ThinhLe279/Battery-Management-System/Design/PCB/PCB.jpg

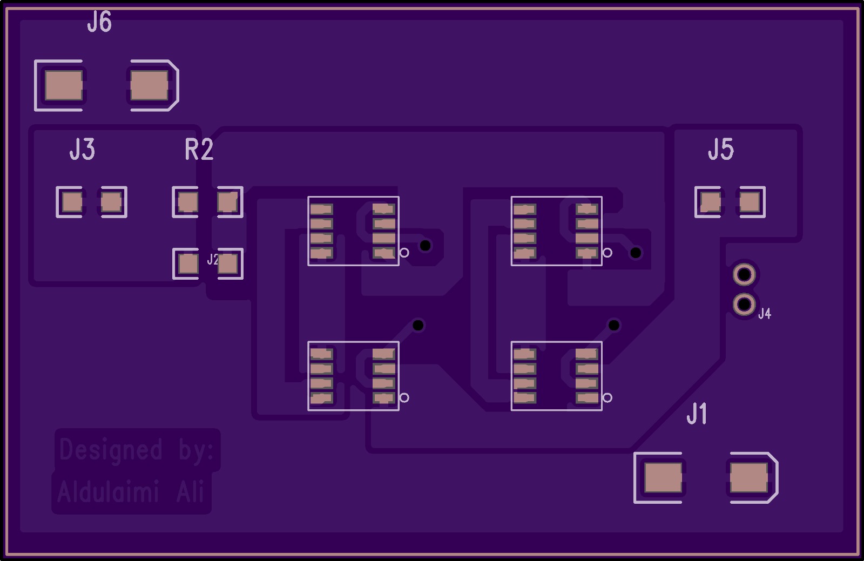
Design/PCB/PCB.jpg
