ThinhLe279/Battery-Management-System/schematic/IMG/Battery Balancing.png

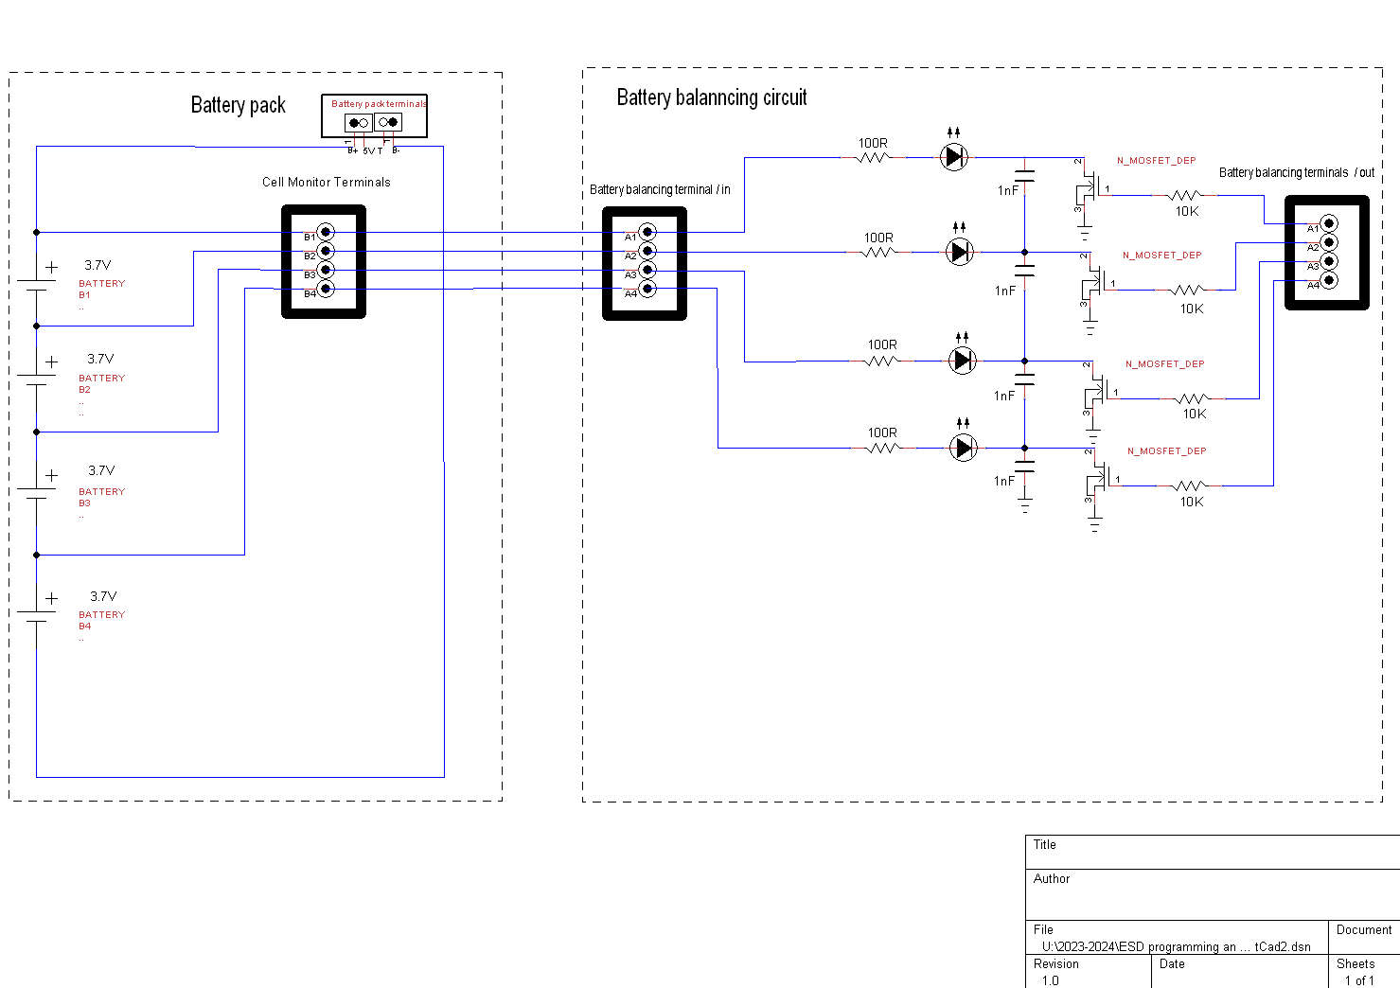
schematic/IMG/Battery Balancing.png
