ThinhLe279/Battery-Management-System/schematic/IMG/MCU power control.png

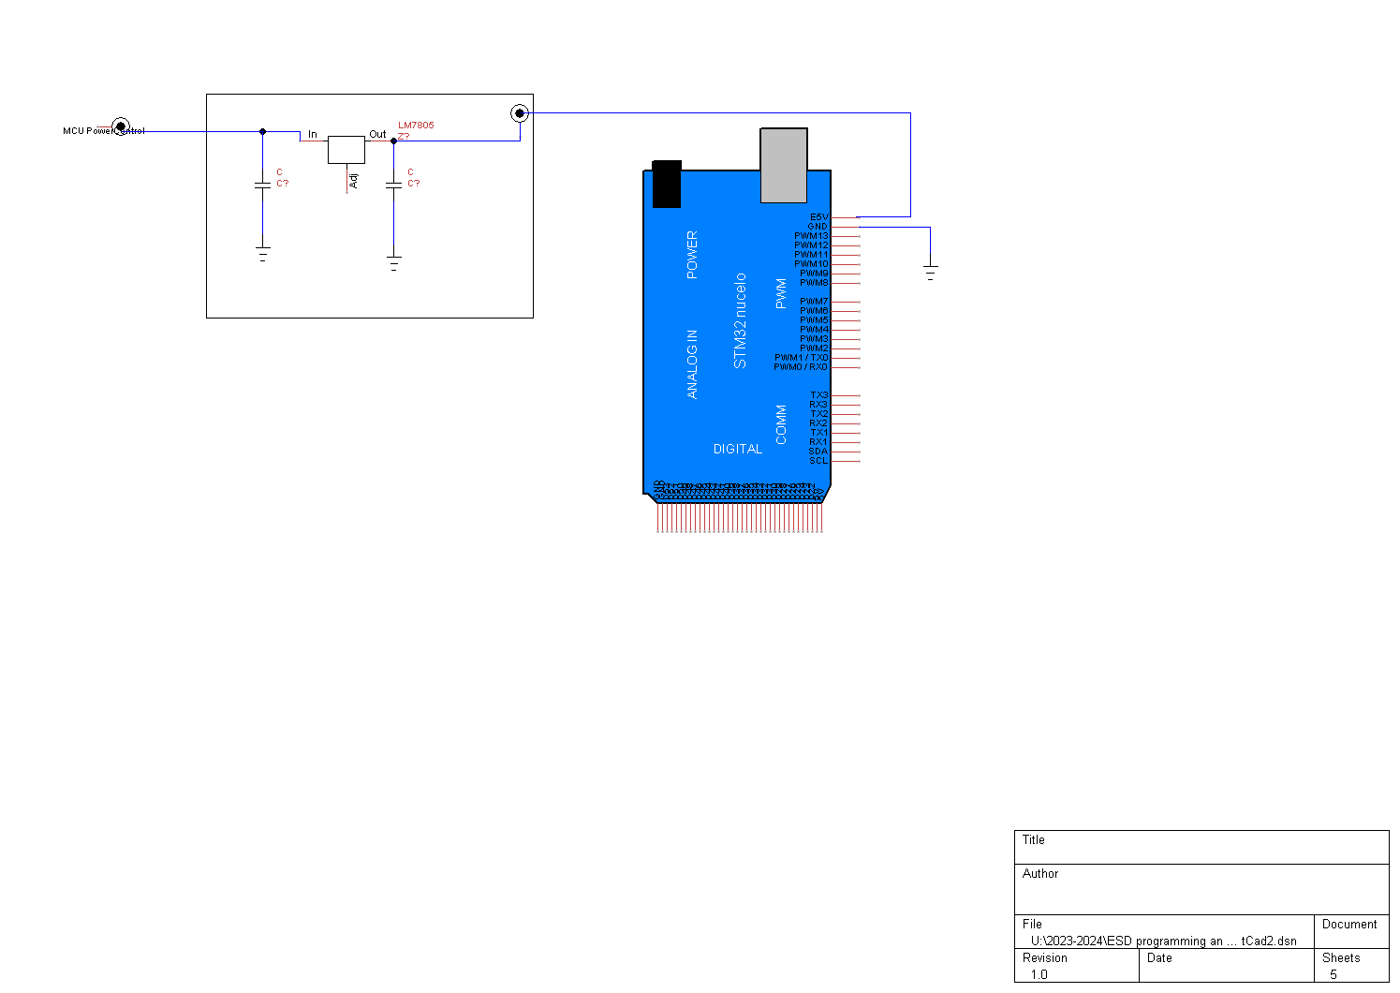
schematic/IMG/MCU power control.png
