ThinhLe279/Battery-Management-System/schematic/IMG/OP-AMP circuit.png

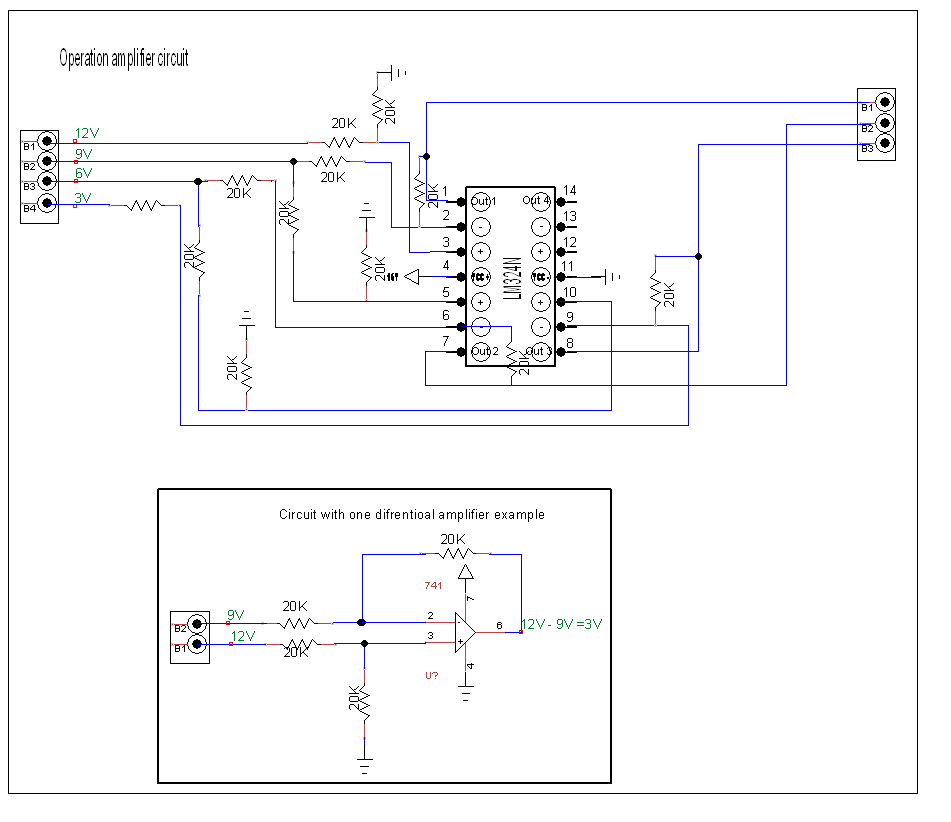
schematic/IMG/OP-AMP circuit.png
