ThinhLe279/Battery-Management-System/Simulation/15_5_voltage_output.PNG

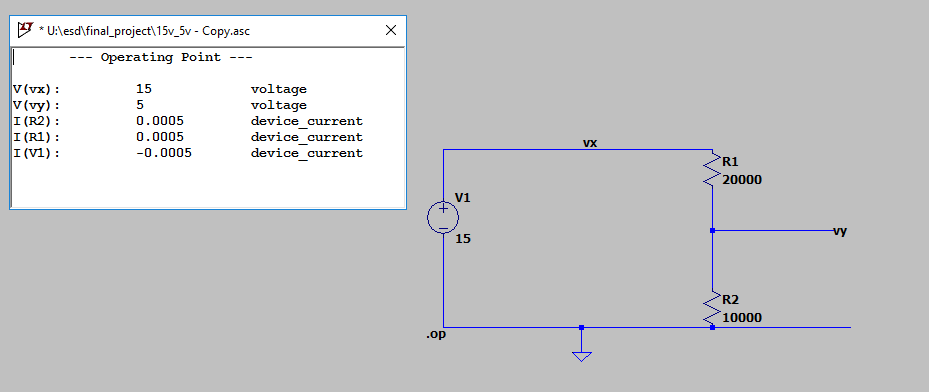
Simulation/15_5_voltage_output.PNG
