ThinhLe279/Battery-Management-System/Simulation/Simulation.PNG

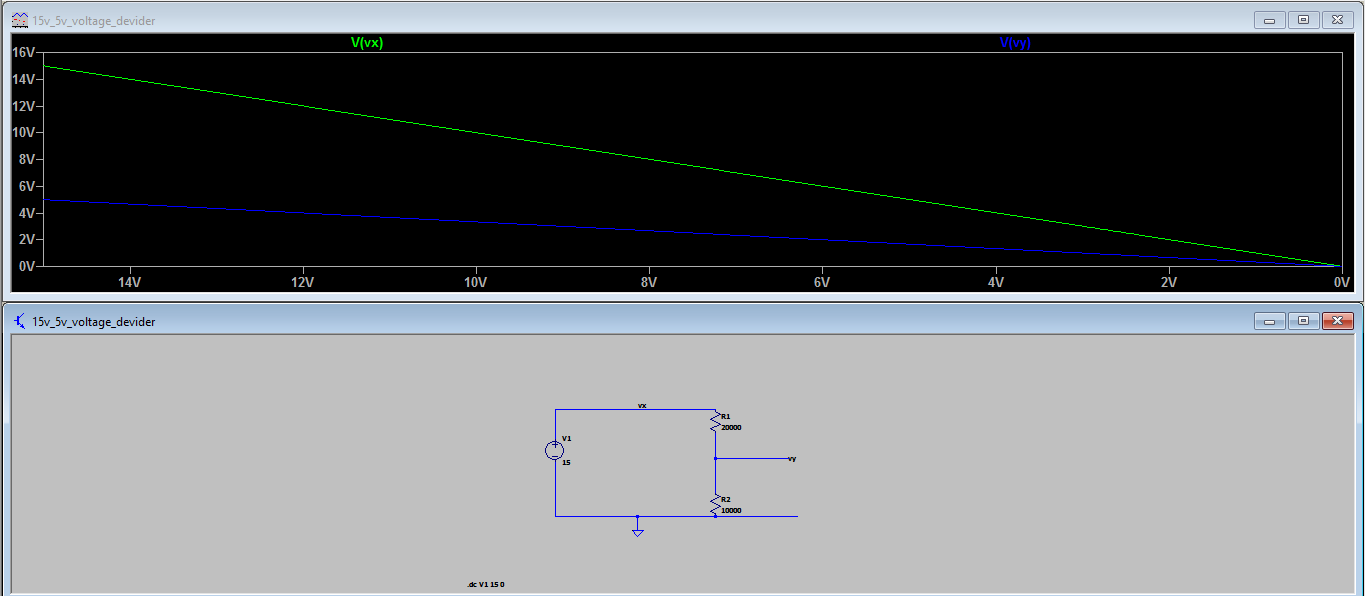
Simulation/Simulation.PNG
