ThinhLe279/Battery-Management-System/Simulation/15v_5v_voltage_devider.asc

R1: res; 40000
R2: res; 10000
V1: voltage; 15
Named nets: 0, vx, vy
.dc V1 0 15
