ThinhLe279/Battery-Management-System/firmware/ADC_measurement.h

/*
 *
 *  Created on: Nov, 2023
 *      Author: Thinh Le
 */

#ifndef PROTOTYPE_H_
#define PROTOTYPE_H_

#include "stm32l1xx.h"

#define TS_CAL1 *((uint16_t *)0x1FF800FA) // TS_CAL1 for the internal temp sensor
#define TS_CAL2 *((uint16_t *)0x1FF800FE) // TS_CAL2 for the internal temp sensor

#define Select_Pin_B 5		// multiplexer selection pin
#define Select_Pin_A 6		// multiplexer selection pin

void Adc_set_up();

void Mux_set_up();

void MFET_set_up();

void Select_mux_pin(int channel);

float Read_Cell_Voltage(void);

float Read_shunt_resistor(void);

float Internal_Temp_Read();

float LM35_Temp_read();

void delay_Ms(int delay);

#endif /* PROTOTYPE_H_ */
